RigoHoward/groove-coaster-printable-shell/STLS/JOYSTICK/Joy_Base_x2.stl

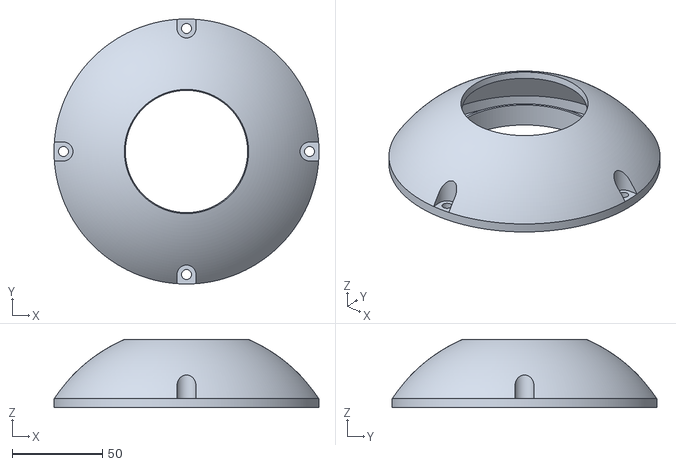
[picture p19: CAD file, 2024-07-12]
STLS/JOYSTICK/Joy_Base_x2.stl
146.7 x 146.7 x 37.7
