RigoHoward/groove-coaster-printable-shell/STLS/PLATES/Center_Bottom_Plate.stl

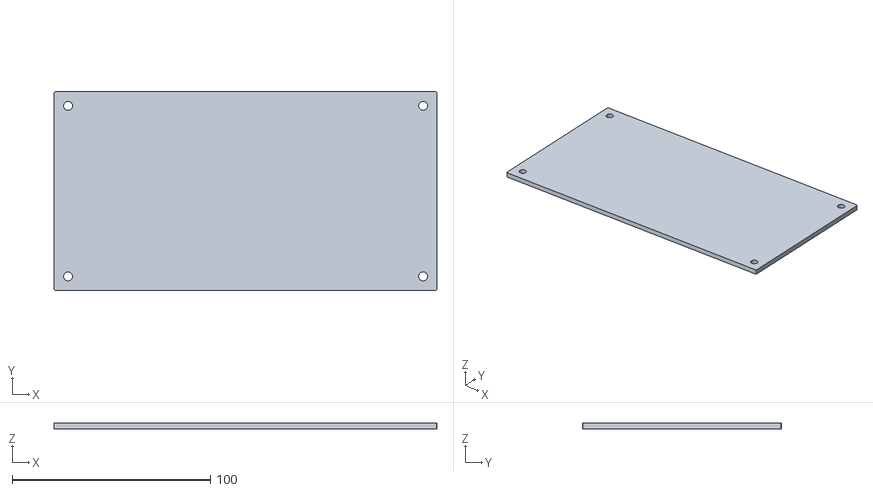
[picture p20: CAD file, 2024-07-12]
STLS/PLATES/Center_Bottom_Plate.stl
193.1 x 100.3 x 3.00
