RigoHoward/groove-coaster-printable-shell/STLS/FRAME/Frame_spacer_x2.stl

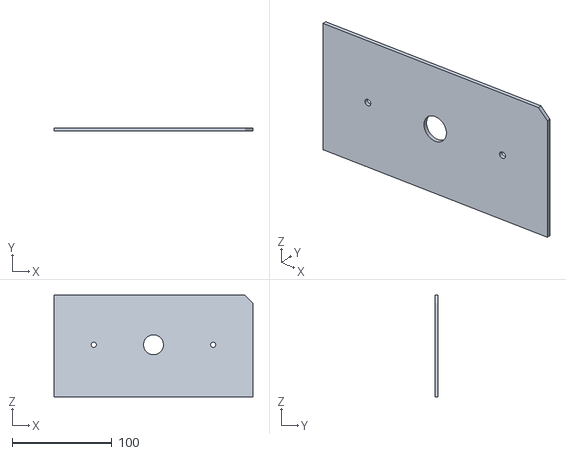
[picture p21: CAD file, 2024-07-12]
STLS/FRAME/Frame_spacer_x2.stl
200.0 x 3.00 x 102.4
