RigoHoward/groove-coaster-printable-shell/STLS/INSERTS/Center_Frame/START/A_start.stl

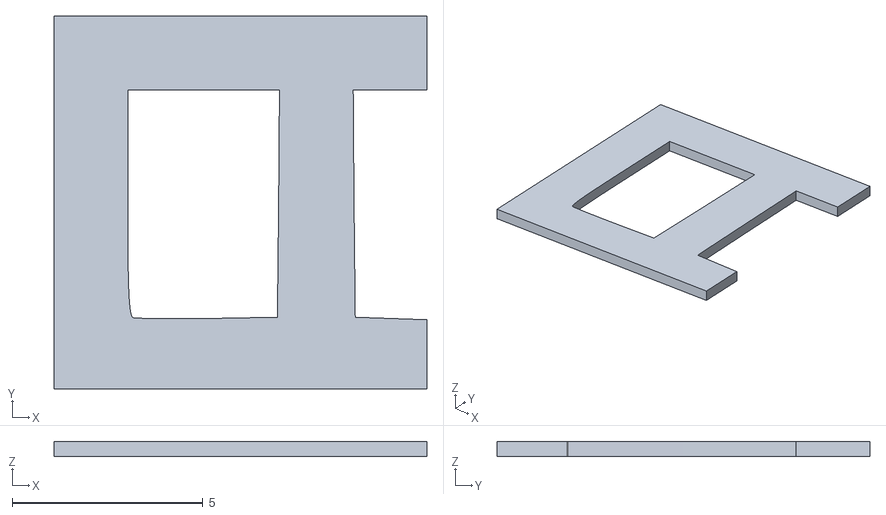
[picture p22: CAD file, 2024-07-12]
STLS/INSERTS/Center_Frame/START/A_start.stl
9.79 x 9.79 x 0.4
