RigoHoward/groove-coaster-printable-shell/STLS/INSERTS/Left_Front_Plate/GROOVE/G_groove.stl

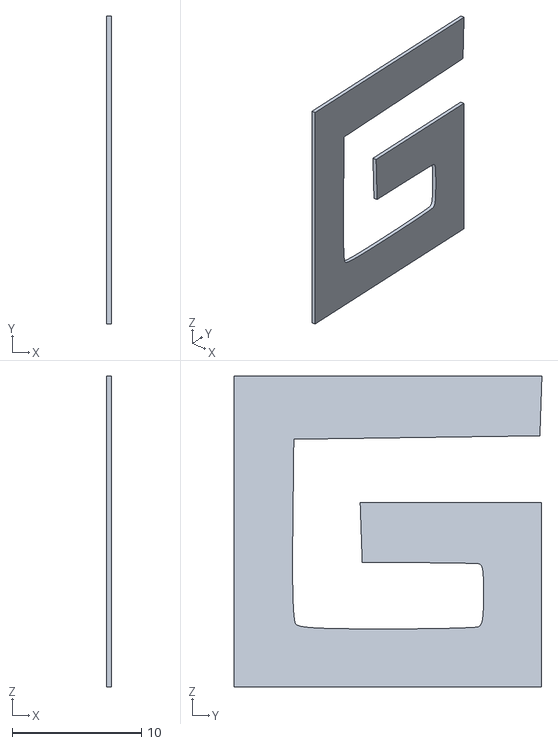
[picture p23: CAD file, 2024-07-12]
STLS/INSERTS/Left_Front_Plate/GROOVE/G_groove.stl
0.4 x 23.8 x 24.1
