RigoHoward/groove-coaster-printable-shell/STLS/INSERTS/Right_Front_Plate/COASTER/A_coaster.stl

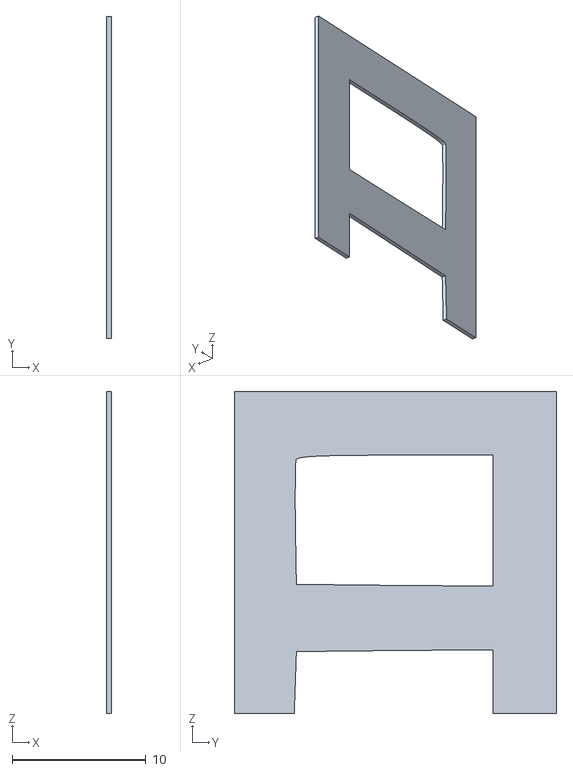
[picture p24: CAD file, 2024-07-12]
STLS/INSERTS/Right_Front_Plate/COASTER/A_coaster.stl
0.4 x 24.1 x 24.1
