RigoHoward/groove-coaster-printable-shell/STLS/JOYSTICK/Joy_Tube_x2.stl

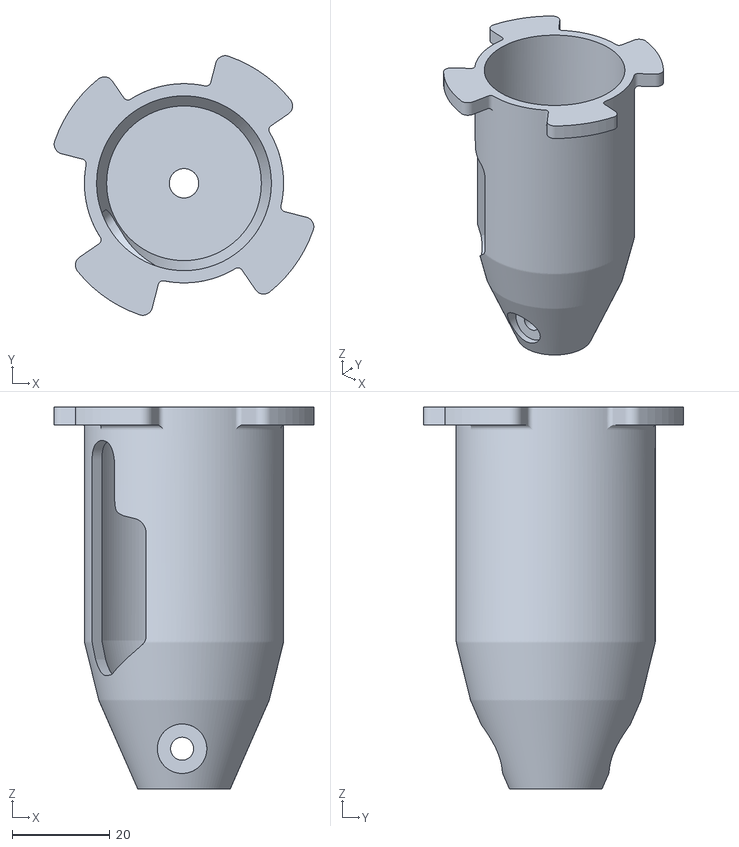
[picture p25: CAD file, 2024-07-12]
STLS/JOYSTICK/Joy_Tube_x2.stl
53.0 x 53.0 x 78.0
