RigoHoward/groove-coaster-printable-shell/STLS/PLATES/Logo_Plate.stl

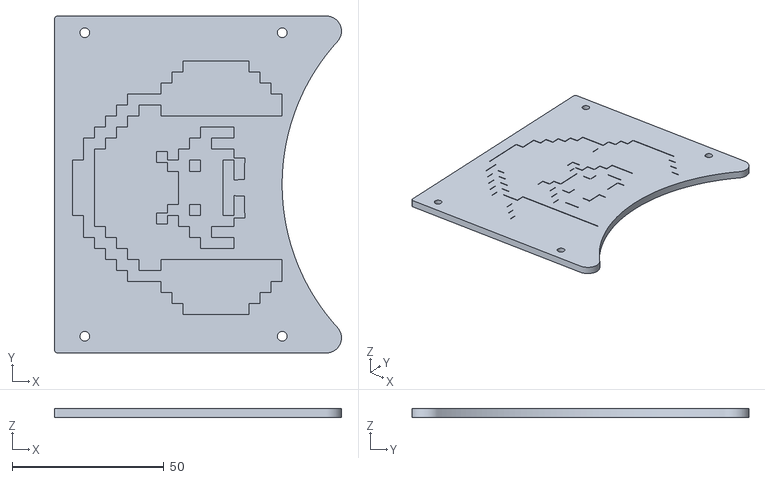
[picture p26: CAD file, 2024-07-12]
STLS/PLATES/Logo_Plate.stl
94.5 x 111.0 x 3.00
