RigoHoward/groove-coaster-printable-shell/STLS/FRAME/Center_Frame.stl

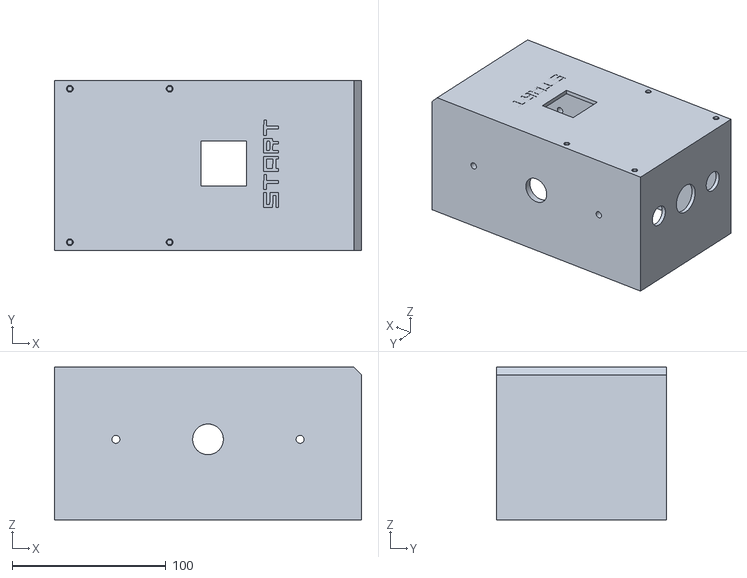
[picture p27: CAD file, 2024-07-12]
STLS/FRAME/Center_Frame.stl
200.0 x 111.0 x 99.4
