RigoHoward/groove-coaster-printable-shell/STLS/INSERTS/Center_Frame/START/T1_start.stl

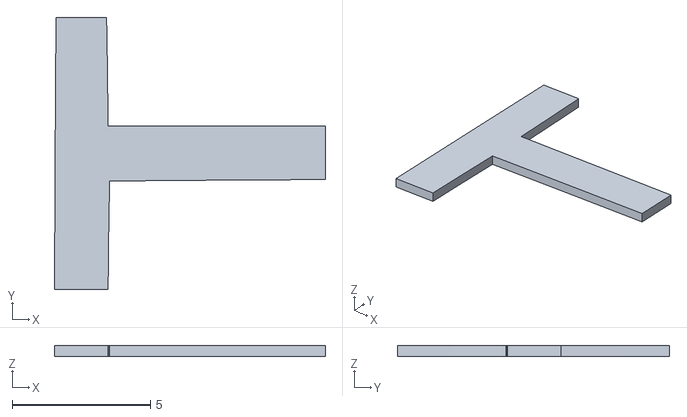
[picture p28: CAD file, 2024-07-12]
STLS/INSERTS/Center_Frame/START/T1_start.stl
9.79 x 9.84 x 0.4
