RigoHoward/groove-coaster-printable-shell/STLS/INSERTS/Left_Frame/L_2.stl

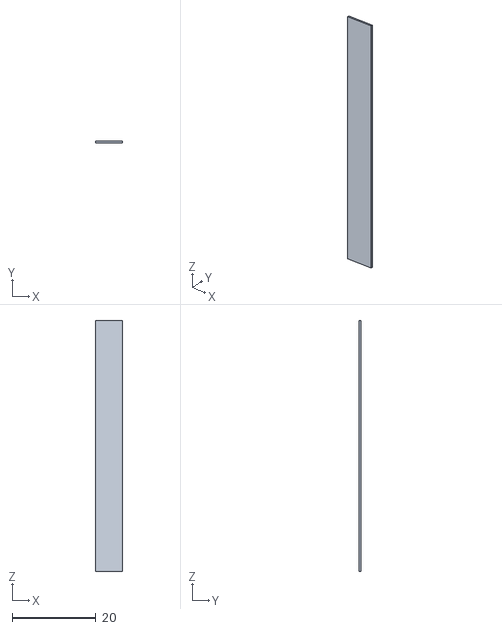
[picture p29: CAD file, 2024-07-12]
STLS/INSERTS/Left_Frame/L_2.stl
6.37 x 0.4 x 59.8
