RigoHoward/groove-coaster-printable-shell/STLS/INSERTS/Left_Front_Plate/GROOVE/O2_groove.stl

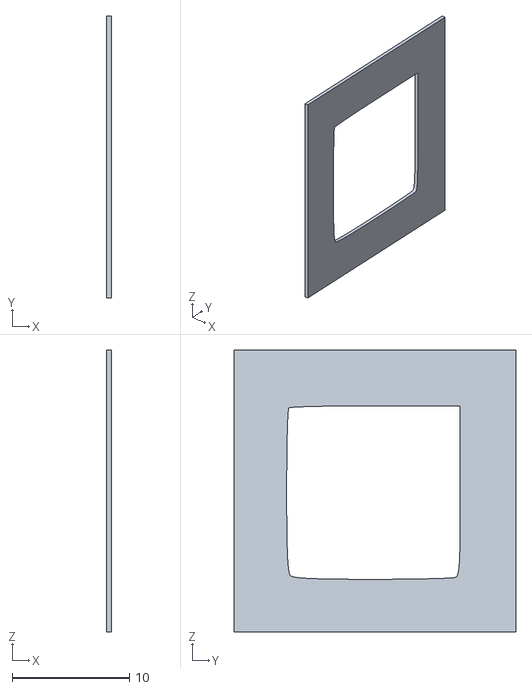
[picture p30: CAD file, 2024-07-12]
STLS/INSERTS/Left_Front_Plate/GROOVE/O2_groove.stl
0.4 x 24.1 x 24.1
