RigoHoward/groove-coaster-printable-shell/STLS/INSERTS/Right_Front_Plate/COASTER/O_coaster.stl

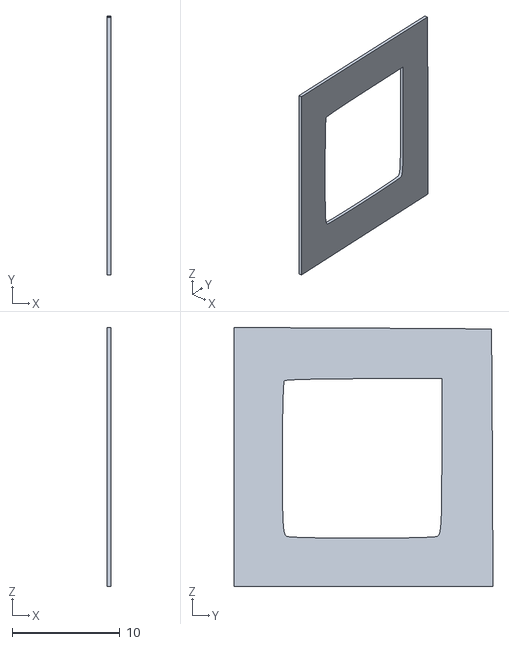
[picture p31: CAD file, 2024-07-12]
STLS/INSERTS/Right_Front_Plate/COASTER/O_coaster.stl
0.4 x 24.1 x 24.1
