RigoHoward/groove-coaster-printable-shell/STLS/JOYSTICK/Joy_Button_x2.stl

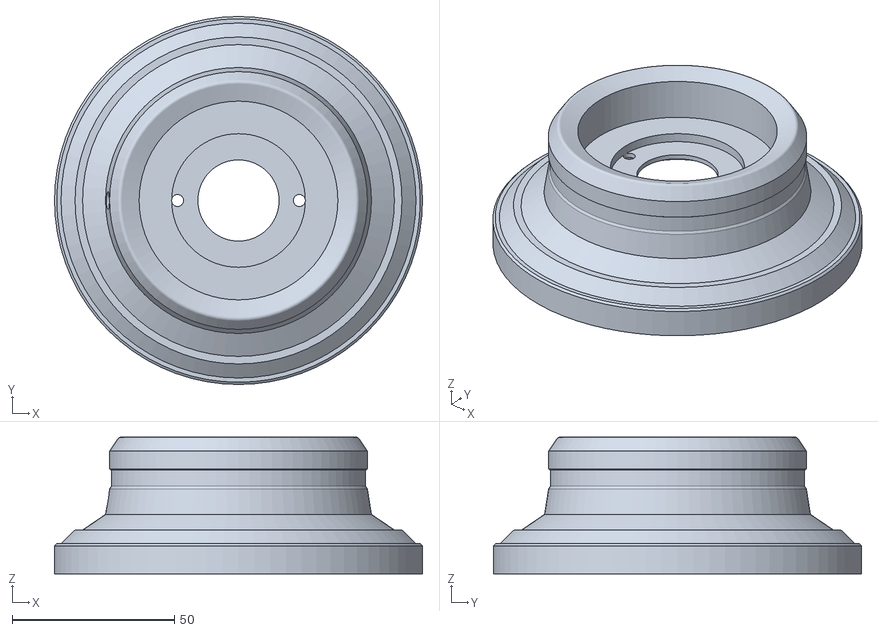
[picture p32: CAD file, 2024-07-12]
STLS/JOYSTICK/Joy_Button_x2.stl
113.3 x 113.3 x 42.0
