RigoHoward/groove-coaster-printable-shell/STLS/PLATES/Right_Bottom_Plate.stl

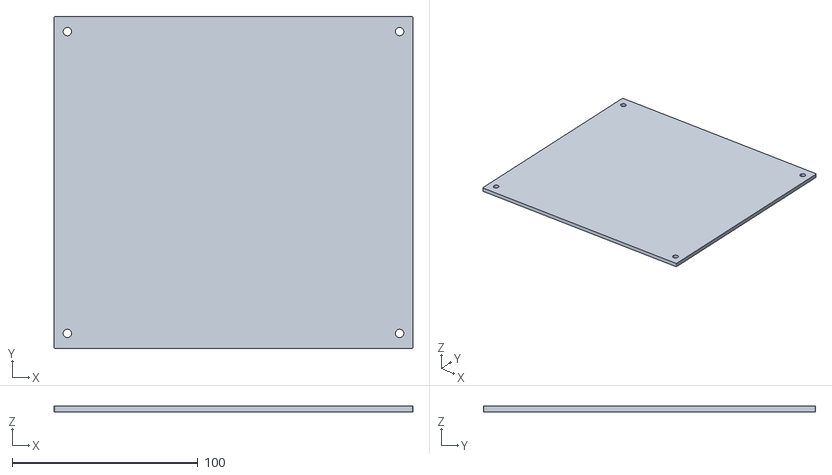
[picture p33: CAD file, 2024-07-12]
STLS/PLATES/Right_Bottom_Plate.stl
193.4 x 179.0 x 3.00
