RigoHoward/groove-coaster-printable-shell/STLS/INSERTS/Left_Frame/L_1.stl

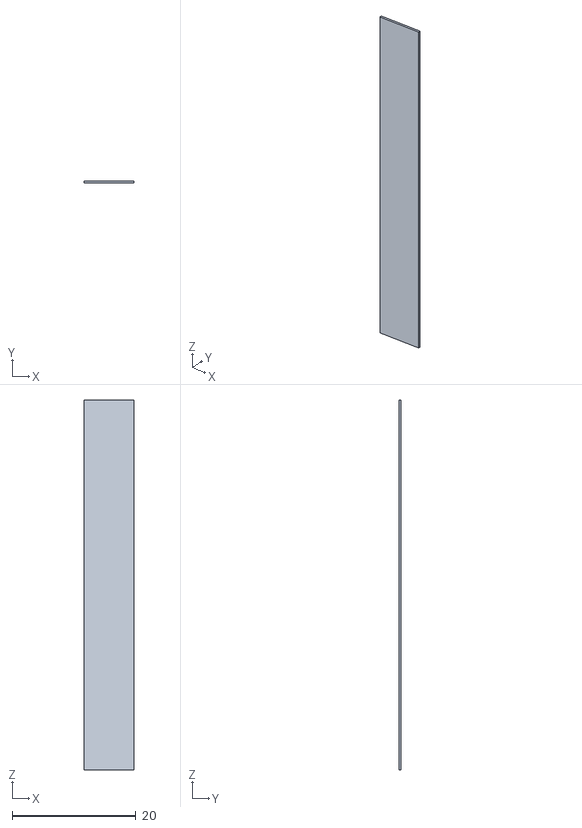
[picture p34: CAD file, 2024-07-12]
STLS/INSERTS/Left_Frame/L_1.stl
8.09 x 0.4 x 59.8
